kasedy/arduino-dc-electronic-dummy-load/doc/3d models/foundation.png

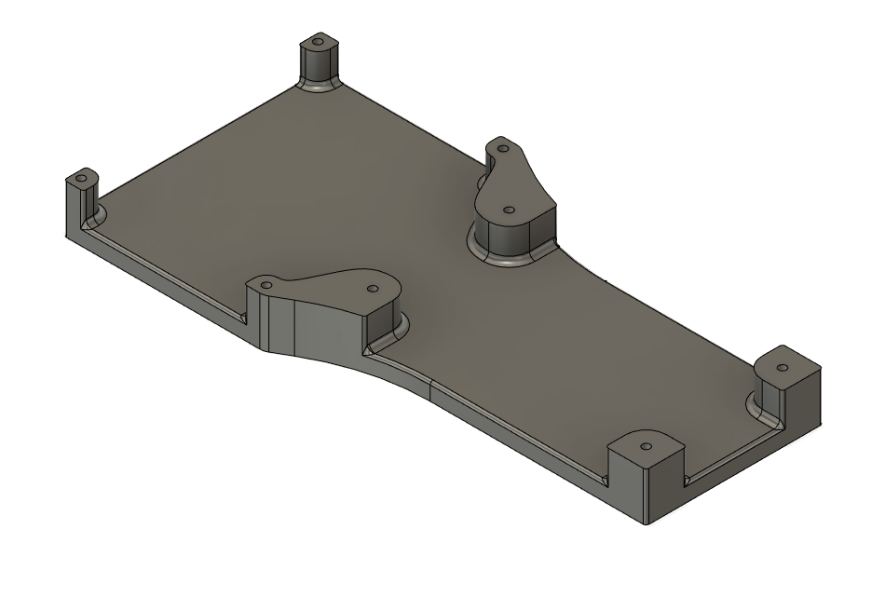
doc/3d models/foundation.png
