kasedy/arduino-dc-electronic-dummy-load/doc/level_1/scheme.png

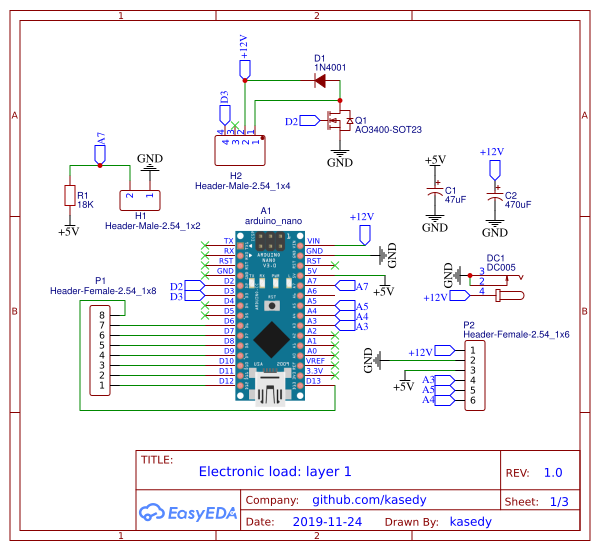
doc/level_1/scheme.png
