kasedy/arduino-dc-electronic-dummy-load/doc/level_2/IMG_20191124_163240353_HDR.jpg

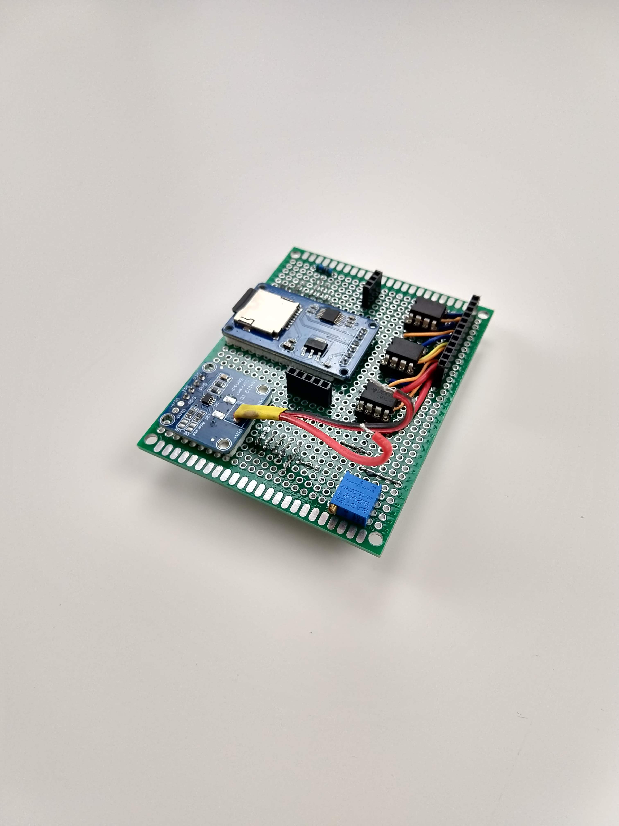
doc/level_2/IMG_20191124_163240353_HDR.jpg
