kasedy/arduino-dc-electronic-dummy-load/doc/level_3/IMG_20191124_163801468_HDR.jpg

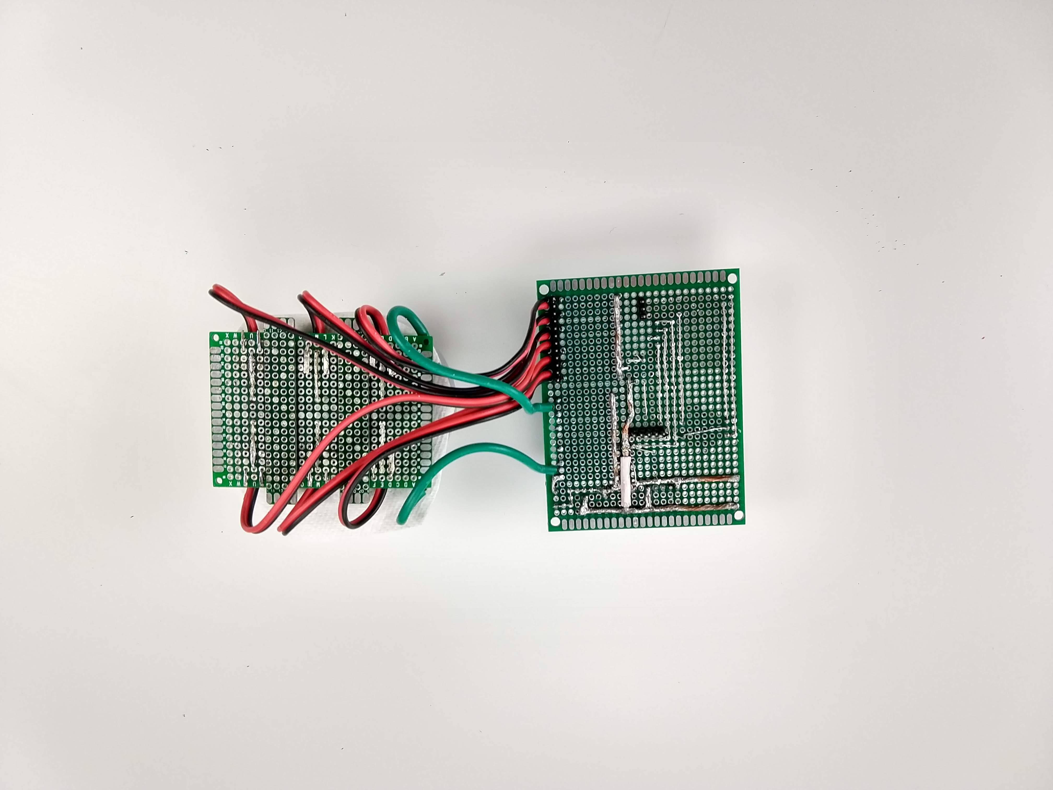
doc/level_3/IMG_20191124_163801468_HDR.jpg
