kasedy/arduino-dc-electronic-dummy-load/doc/level_3/IMG_20191124_163842153_HDR.jpg

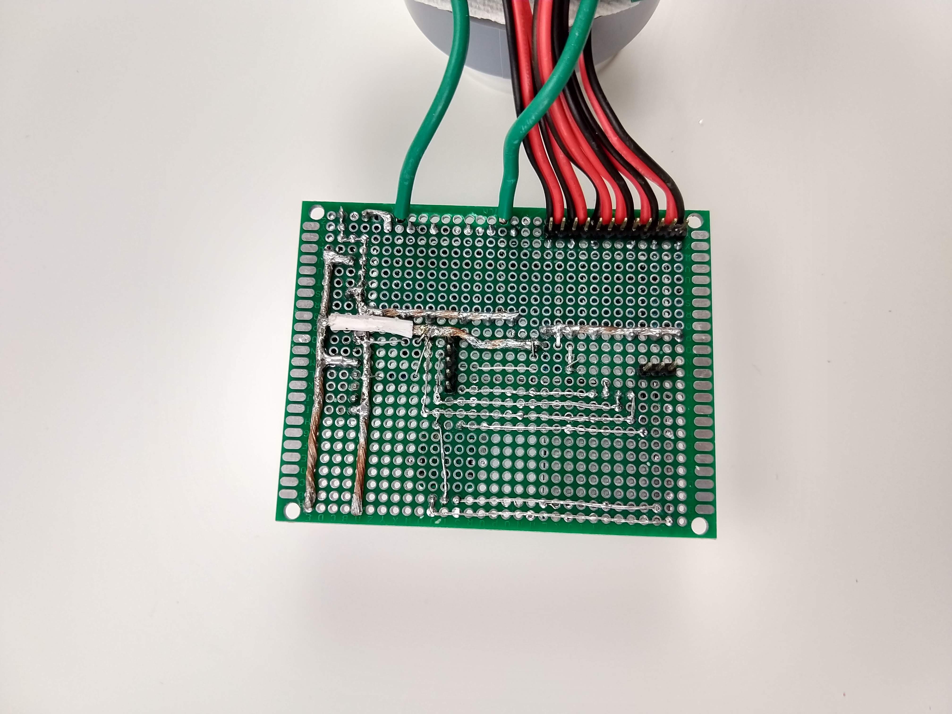
doc/level_3/IMG_20191124_163842153_HDR.jpg
