kasedy/arduino-dc-electronic-dummy-load/doc/load/IMG_20191124_163354215_HDR.jpg

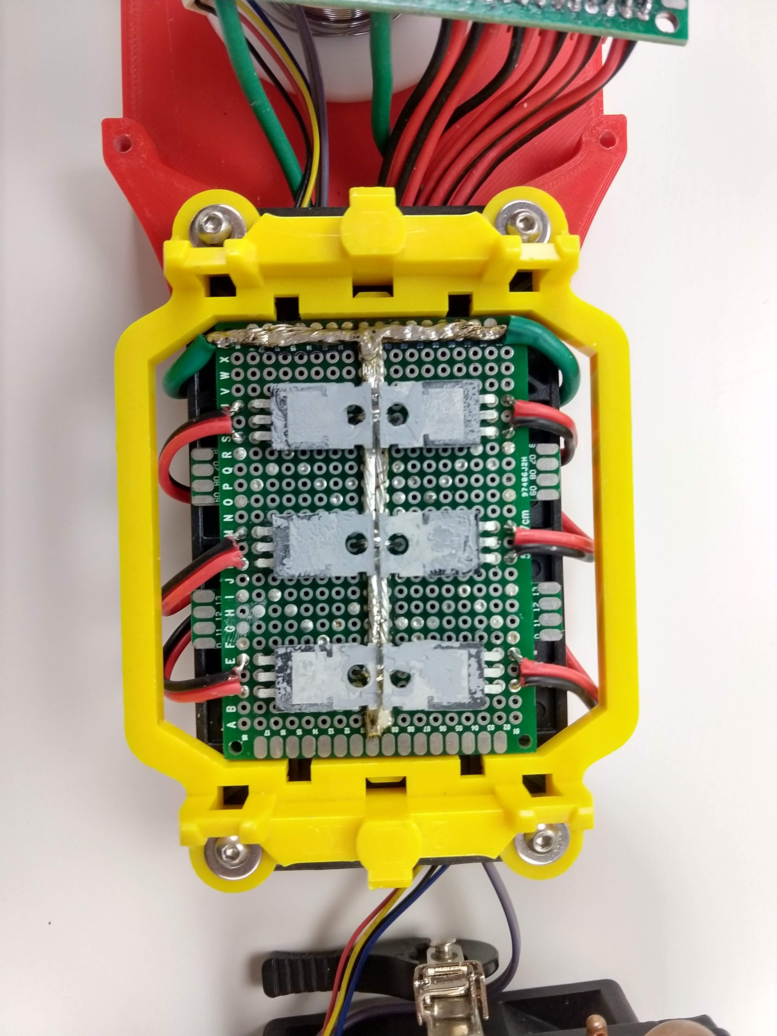
doc/load/IMG_20191124_163354215_HDR.jpg
