kasedy/arduino-dc-electronic-dummy-load/doc/level_1/wiring.jpg

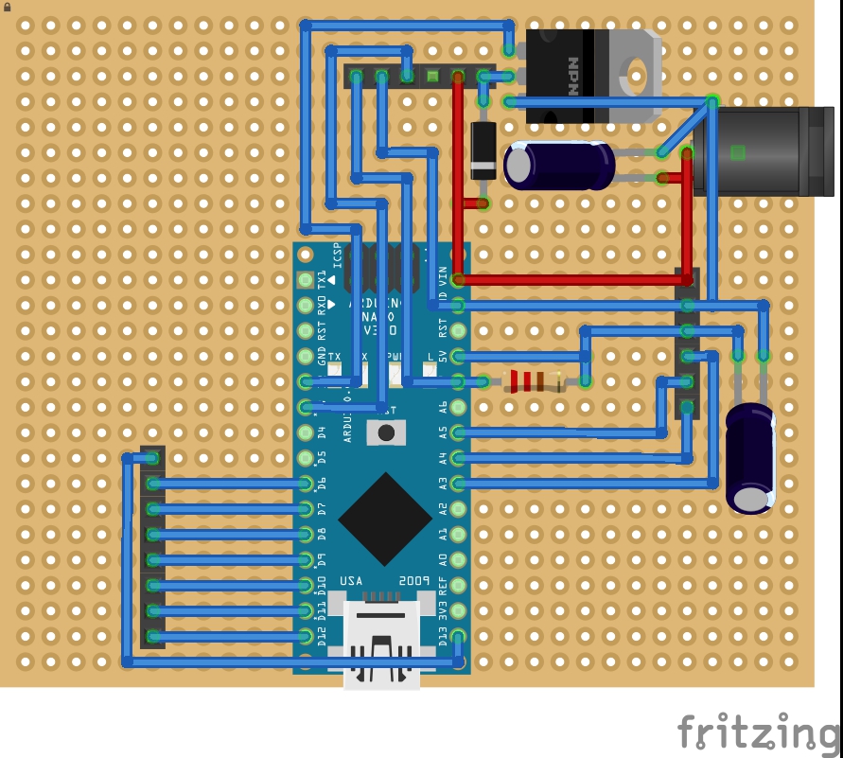
doc/level_1/wiring.jpg
